msx-solis/F4-FMPACv2/pictures/IMG_20210916_0124205.jpg

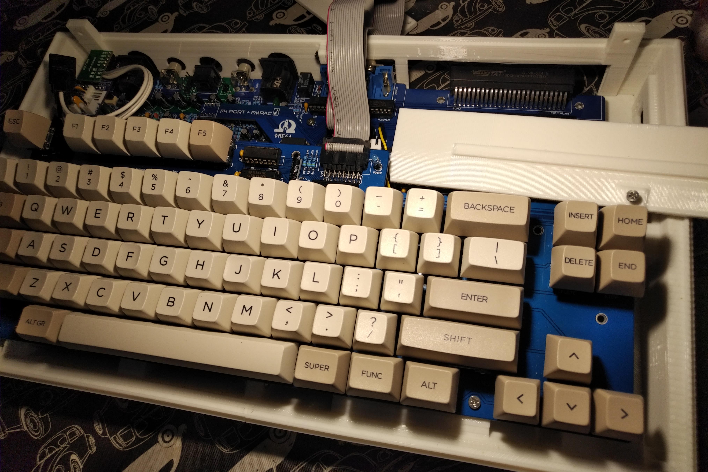
pictures/IMG_20210916_0124205.jpg
